prittt/sump-controller/imgs/Img 03.jpeg

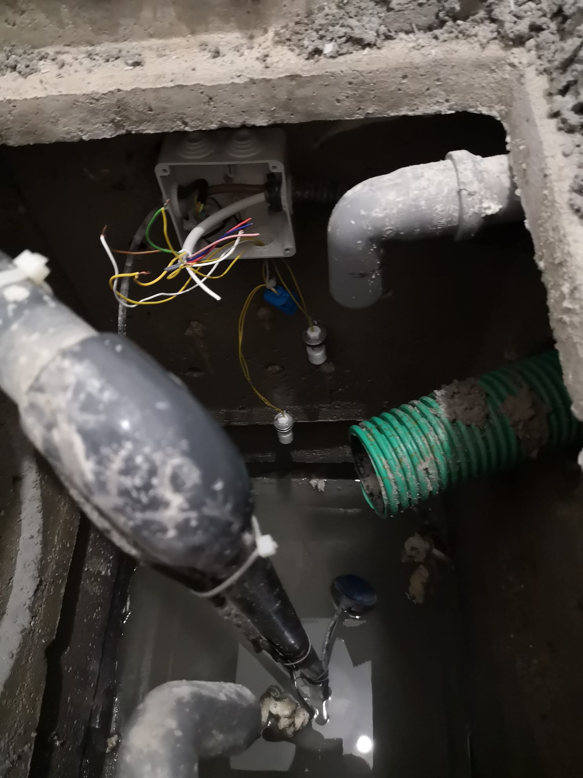
imgs/Img 03.jpeg
