prittt/sump-controller/imgs/Img 06.jpeg

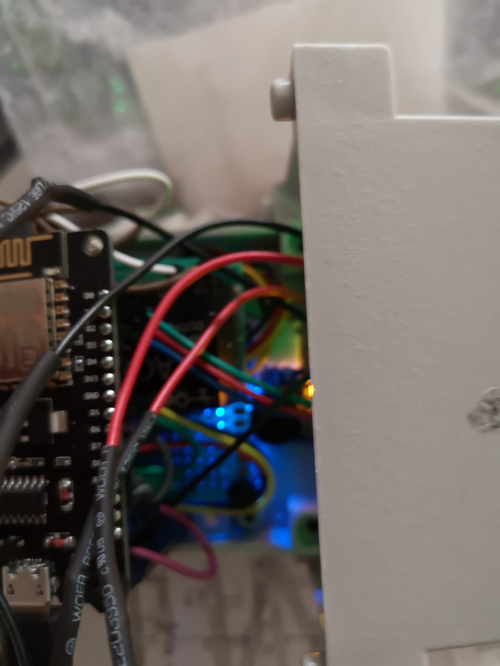
imgs/Img 06.jpeg
