prittt/sump-controller/imgs/Img 07.jpeg

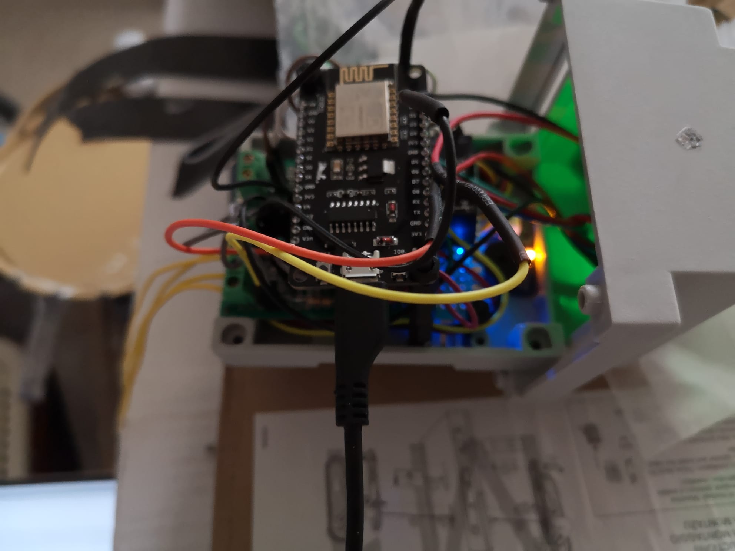
imgs/Img 07.jpeg
