prittt/sump-controller/imgs/Img 08.jpeg

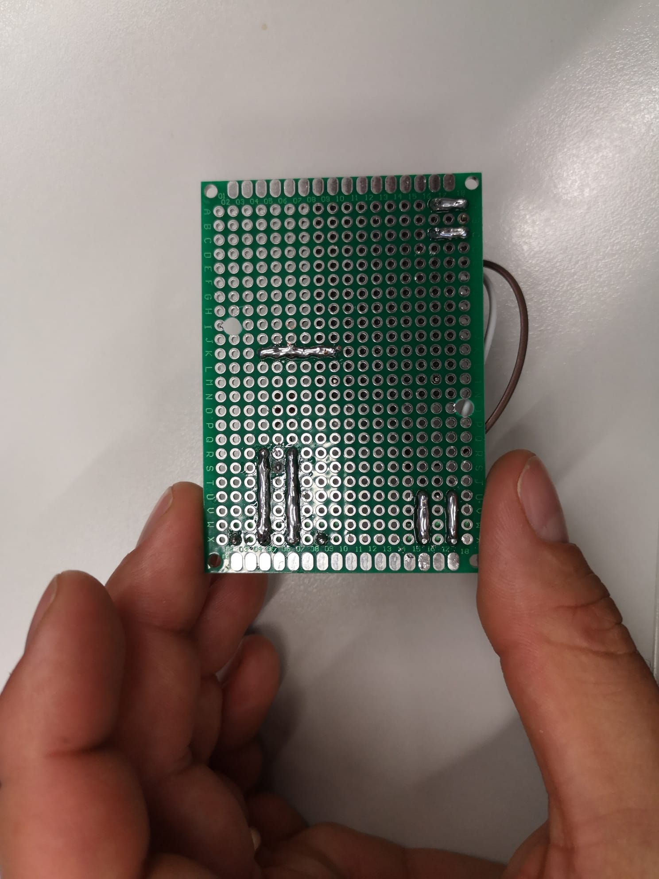
imgs/Img 08.jpeg
