prittt/sump-controller/imgs/Img 09.jpeg

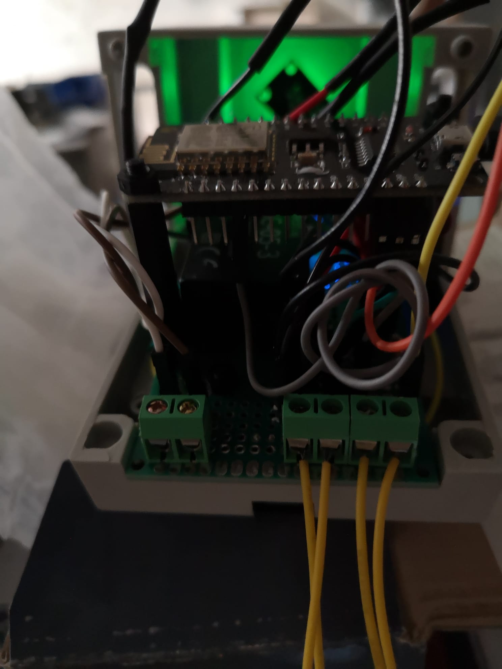
imgs/Img 09.jpeg
